G4lile0/Arduino_3dprinted_Lunar_Phase_Clock/images/11-14-10.16.31.jpg

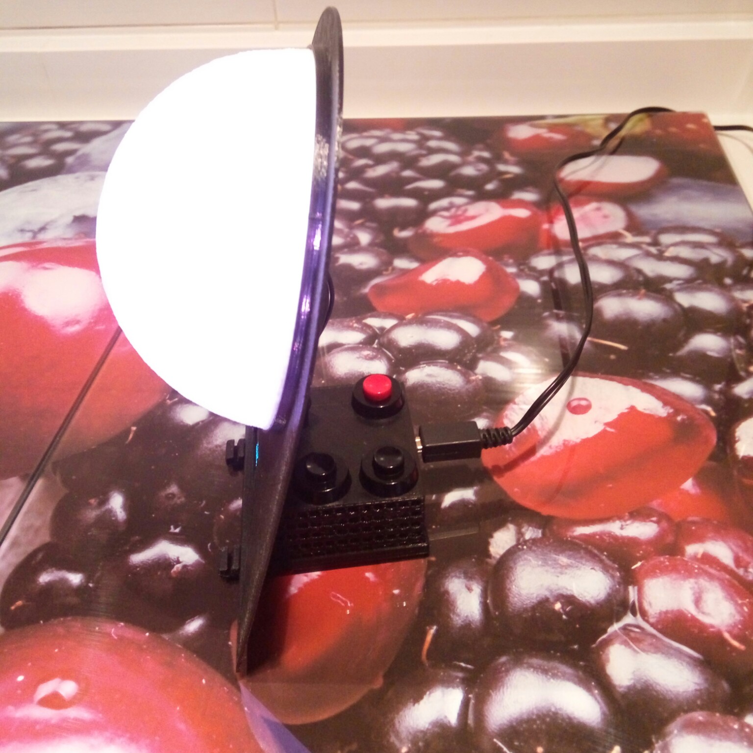
images/11-14-10.16.31.jpg
