G4lile0/Arduino_3dprinted_Lunar_Phase_Clock/images/103_0706.JPG

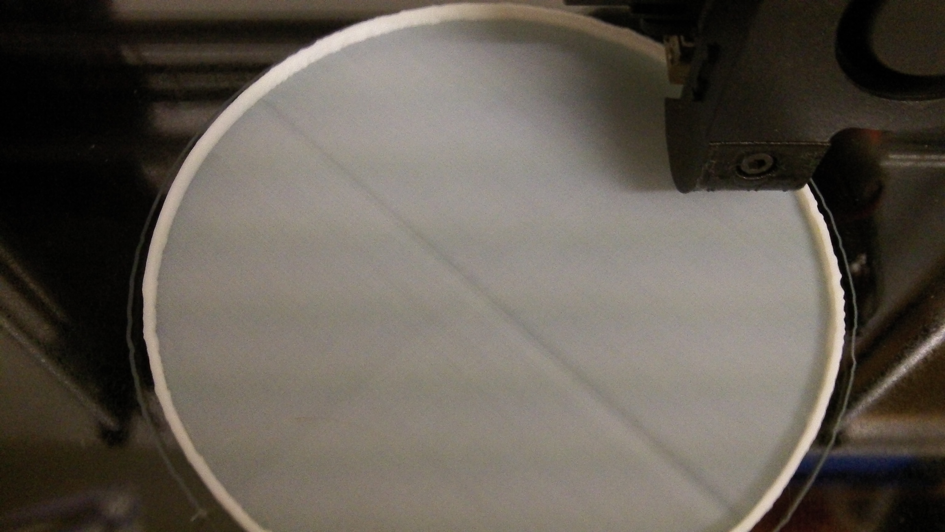
images/103_0706.JPG
