G4lile0/Arduino_3dprinted_Lunar_Phase_Clock/images/Captura de pantalla de 2016-10-10 22-45-52.png

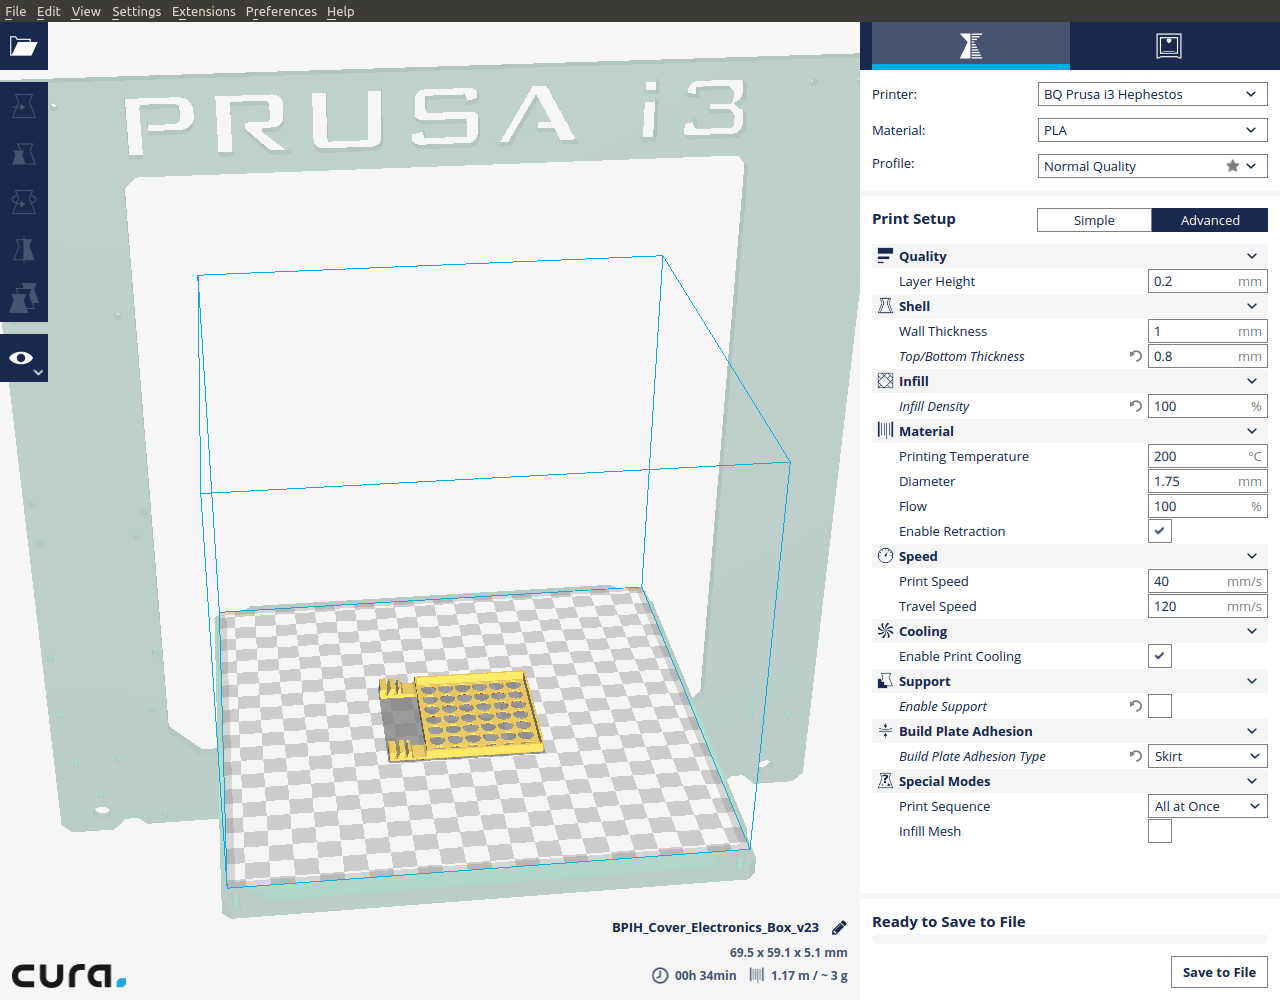
images/Captura de pantalla de 2016-10-10 22-45-52.png
