G4lile0/Arduino_3dprinted_Lunar_Phase_Clock/images/DSC00632.JPG

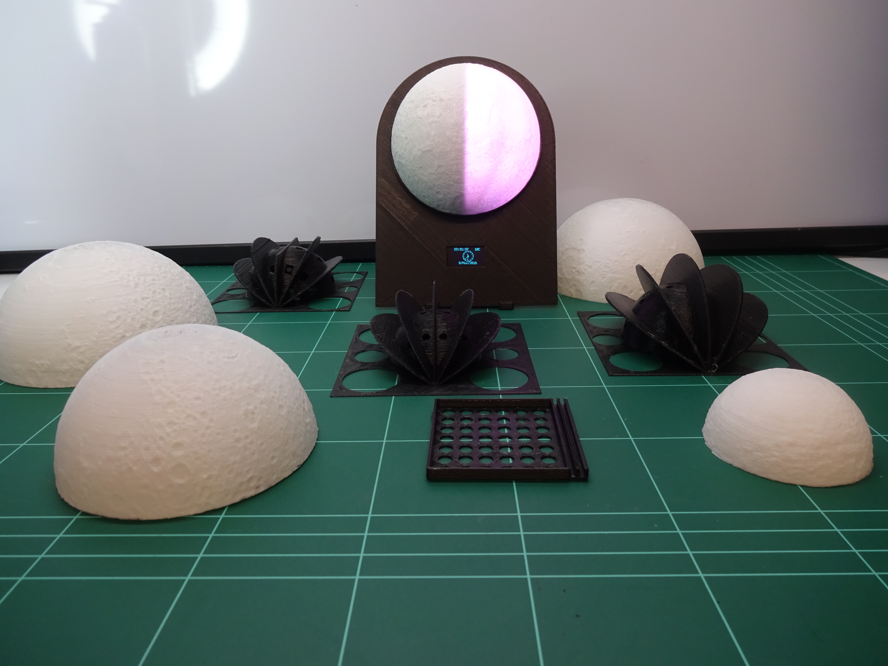
images/DSC00632.JPG
