G4lile0/Arduino_3dprinted_Lunar_Phase_Clock/images/led_support.png

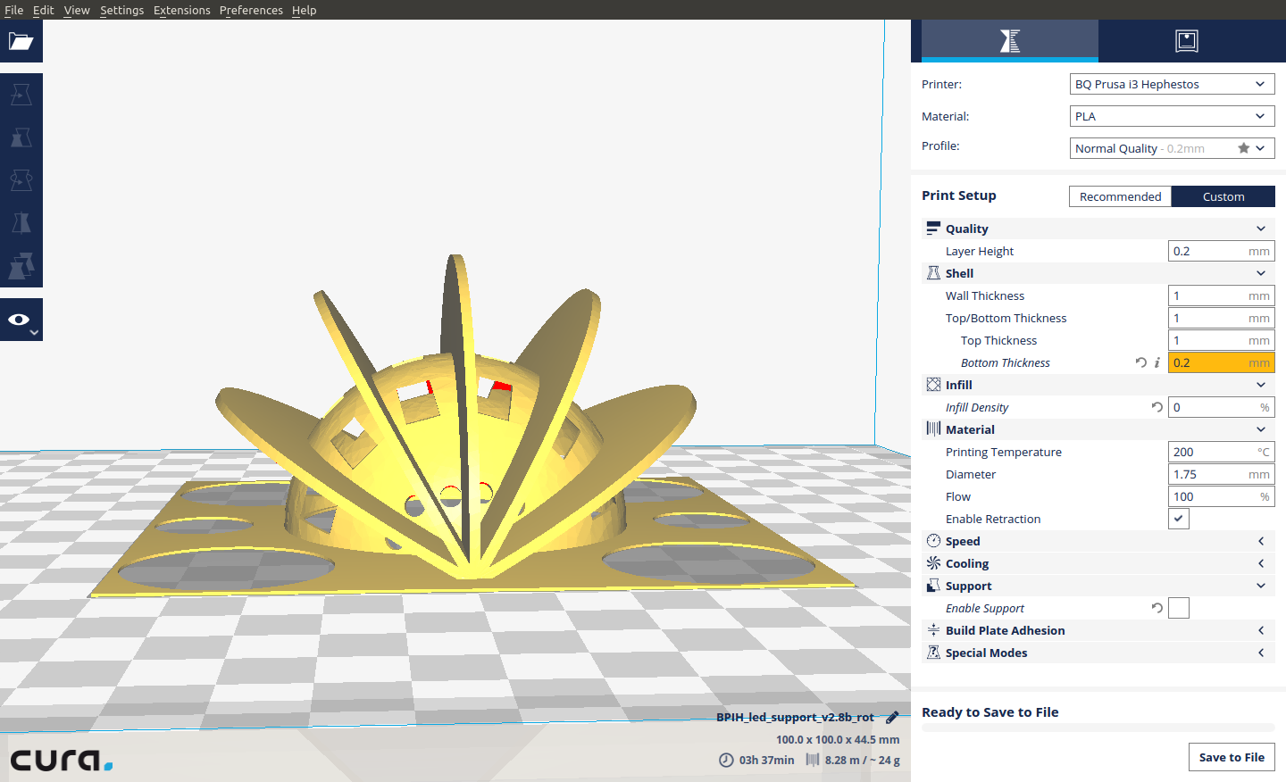
images/led_support.png
