G4lile0/Arduino_3dprinted_Lunar_Phase_Clock/images/moon_support.png

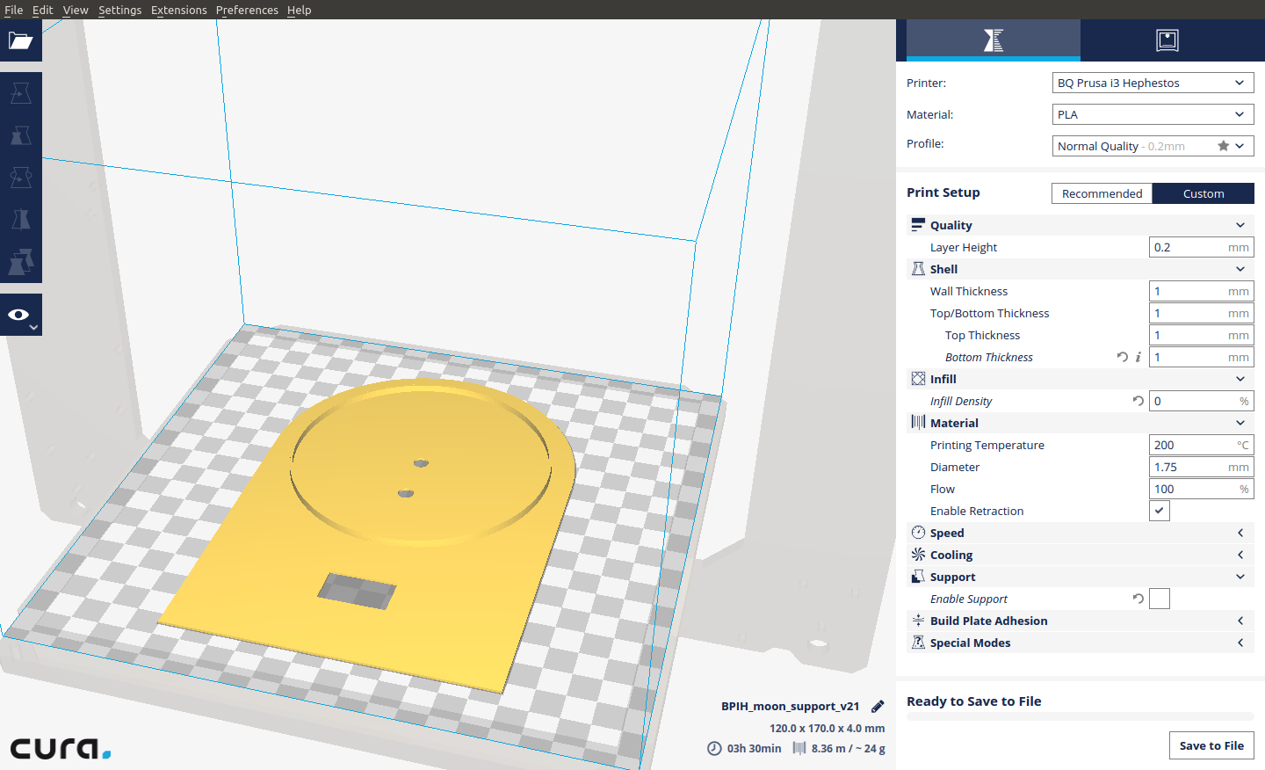
images/moon_support.png
