G4lile0/Arduino_3dprinted_Lunar_Phase_Clock/images/photo1.jpg

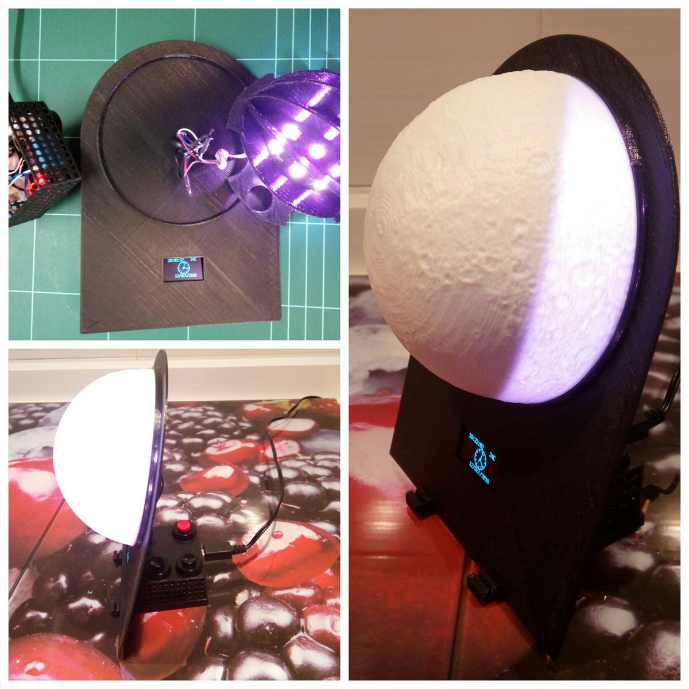
images/photo1.jpg
