G4lile0/Arduino_3dprinted_Lunar_Phase_Clock/images/PicsArt_10-09-10.36.12.jpg

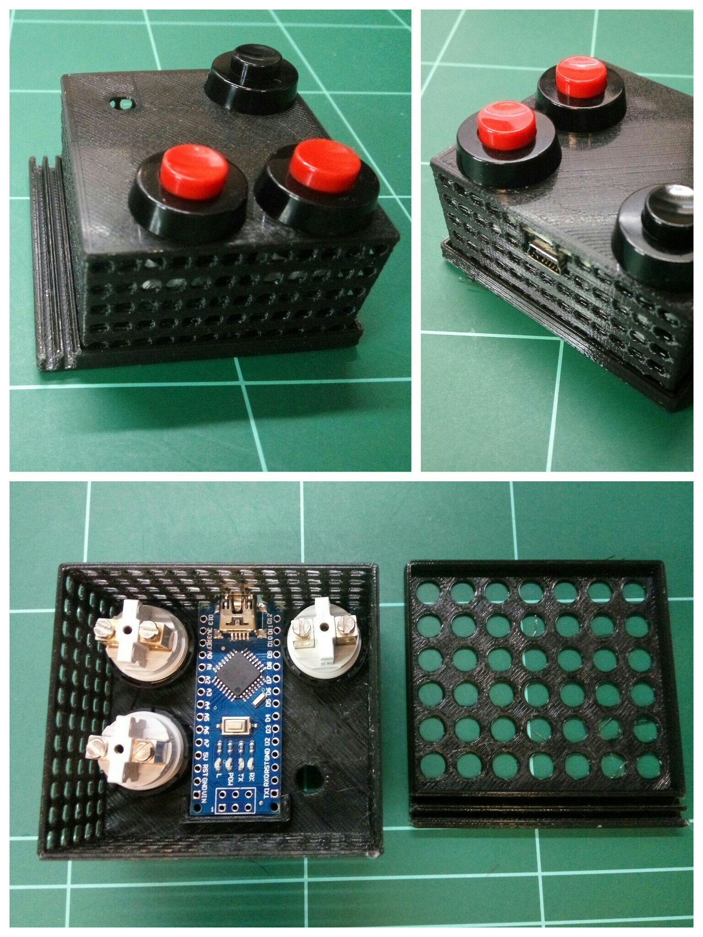
images/PicsArt_10-09-10.36.12.jpg
